dupontgu/hidden_agenda_pedal/firmware/src/tud_callbacks.cpp

#include <stdlib.h>
#include <stdio.h>
#include "tusb.h"

// These are all effectively no-ops, just keeping them out of the way for now.

//--------------------------------------------------------------------+
// USB HID
//--------------------------------------------------------------------+

// Invoked when received GET_REPORT control request
// Application must fill buffer report's content and return its length.
// Return zero will cause the stack to STALL request
uint16_t tud_hid_get_report_cb(uint8_t instance, uint8_t report_id,
                               hid_report_type_t report_type, uint8_t* buffer,
                               uint16_t reqlen) {
  (void)instance;
  (void)report_id;
  (void)report_type;
  (void)buffer;
  (void)reqlen;

  return 0;
}

// Invoked when received SET_REPORT control request or
// received data on OUT endpoint ( Report ID = 0, Type = 0 )
void tud_hid_set_report_cb(uint8_t instance, uint8_t report_id,
                           hid_report_type_t report_type, uint8_t const* buffer,
                           uint16_t bufsize) {
  (void)instance;
  (void)report_id;
  (void)report_type;
  (void)buffer;
  (void)bufsize;
}
