dupontgu/hidden_agenda_pedal/firmware/test/test_persistence.hpp

#include "persistence.hpp"

class InMemoryPersistence : public IPersistence {
 public:
  InMemoryPersistence() {}
  void initialize() { resetToDefaults(); }
  uint8_t getVersion() { return 1; }
  void setActiveFxSlot(uint8_t slot) { active_slot = slot; }
  uint8_t getActiveFxSlot() { return active_slot; }
  void setReportParseMode(uint8_t mode) { report_mode = mode; }
  uint8_t getReportParseMode() { return report_mode; }
  void setLedBrightness(float brightness) { led_brightness = brightness; }
  float getLedBrightness() { return led_brightness; }
  void setLedColor(uint8_t slot, uint32_t color) { slots[slot] = color; }
  uint32_t getLedColor(uint8_t slot) { return slots[slot]; }
  void setRawHidLogsEnabled(bool enabled) { raw_hid_logs_enabled = enabled; }
  bool areRawHidLogsEnabled() { return raw_hid_logs_enabled; }
  void setFlashingEnabled(bool enabled) { flashing_enabled = enabled; }
  bool isFlashingEnabled() { return flashing_enabled; }
  void setShouldInvertFootswitch(bool invert) { invert_footswitch = invert; }
  bool shouldInvertFootswitch() { return invert_footswitch; }
  void setMouseSpeedLevel(uint8_t level) { mouse_speed_level = level; }
  uint8_t getMouseSpeedLevel() { return mouse_speed_level; }
  void resetToDefaults() {
    active_slot = 0;
    report_mode = 0;
    mouse_speed_level = 0;
    raw_hid_logs_enabled = false;
    flashing_enabled = true;
    invert_footswitch = false;
    led_brightness = 0.0f;
    slots[0] = 0;
    slots[1] = 0;
    slots[2] = 0;
    slots[3] = 0;
  }

 private:
  uint8_t active_slot;
  uint8_t report_mode;
  uint8_t mouse_speed_level;
  bool raw_hid_logs_enabled;
  bool flashing_enabled;
  bool invert_footswitch;
  float led_brightness;
  uint32_t slots[4] = {0, 0, 0, 0};
};
